Axsel/a3-control-center-pcb/manufacturing/generated/rev-a-audit/review/back-paste.png

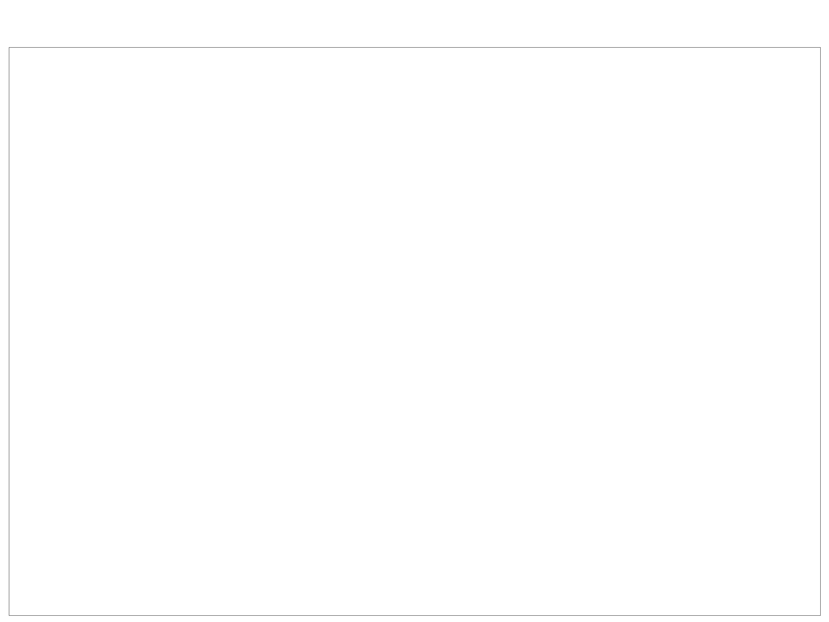
manufacturing/generated/rev-a-audit/review/back-paste.png
