Axsel/a3-control-center-pcb/manufacturing/generated/rev-a-audit/review/back-silkscreen.png

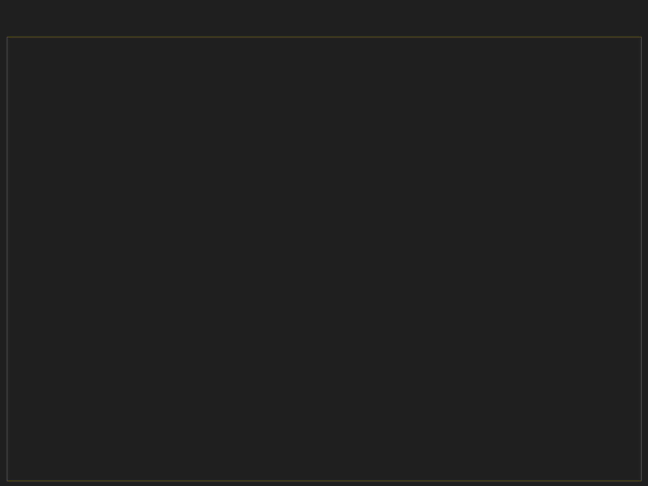
manufacturing/generated/rev-a-audit/review/back-silkscreen.png
