Axsel/a3-control-center-pcb/manufacturing/generated/rev-a-audit/review/front-paste.png

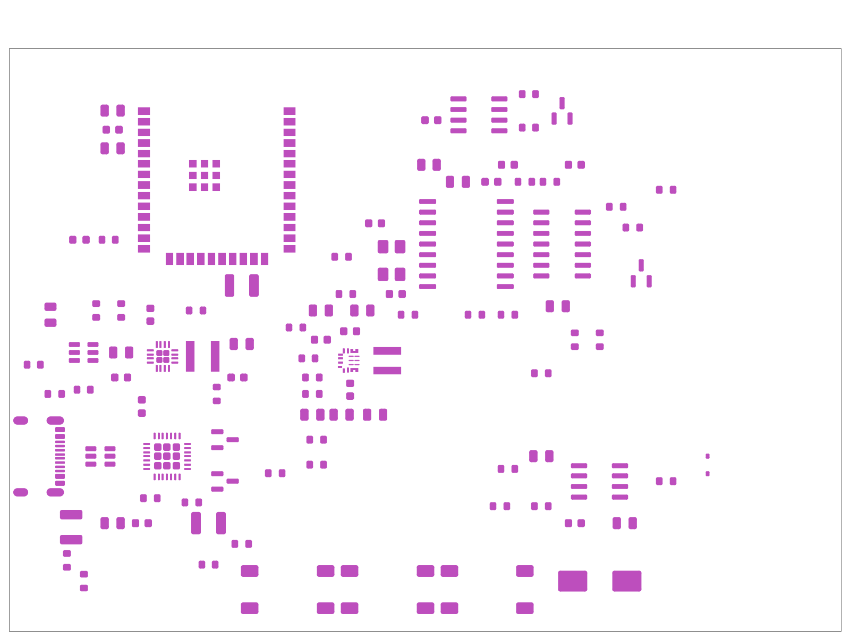
manufacturing/generated/rev-a-audit/review/front-paste.png
