Axsel/a3-control-center-pcb/manufacturing/generated/rev-a-audit/review/inner-gnd.png

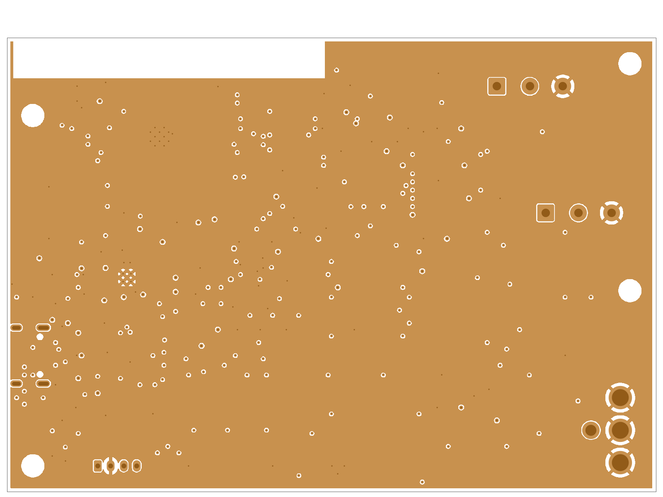
manufacturing/generated/rev-a-audit/review/inner-gnd.png
